nifty-knight/Sunrise-Alarm-Clock-2025/Images/Onshape Pictures/Screenshot 2025-08-16 090349.png

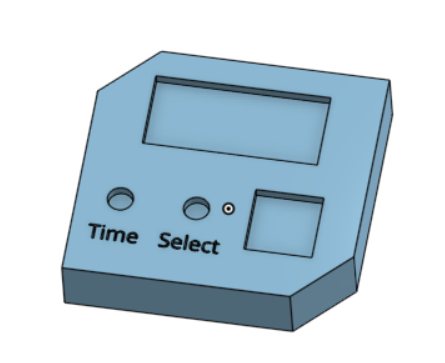
Images/Onshape Pictures/Screenshot 2025-08-16 090349.png
