nifty-knight/Sunrise-Alarm-Clock-2025/src/basic_lcd_print/basic_lcd_print.ino

// include the library
#include <LiquidCrystal.h>

// Creates an LCD object. Parameters: (rs, enable, d4, d5, d6, d7)
LiquidCrystal lcd(13, 11, 10, 8, 3, 2);

void setup() {
  // set up the LCD's number of columns and rows:
  lcd.begin(16, 2);
  // lcd.display();
  pinMode(A5, OUTPUT);
  digitalWrite(A5, 1);

  // Clears the LCD screen
  lcd.clear();
}

void loop() {
  // Print a message to the LCD.
  lcd.print(" Hello world!");

  // set the cursor to column 0, line 1
  // (note: line 1 is the second row, since counting begins with 0):
  lcd.setCursor(0, 1);
  // Print a message to the LCD.
  lcd.print(" LCD Tutorial");
}
