nifty-knight/Sunrise-Alarm-Clock-2025/src/Clock_Module_getTimeExample/Clock_Module_getTimeExample.ino

/** GetDateTime.cpp
 *
 * Example of getting the date and time from the RTC.
 *
 * @version 1.0.1
 * @author Rafa Couto <caligari@treboada.net>
 * @license GNU Affero General Public License v3.0
 * @see https://github.com/Treboada/Ds1302
 *
 */
#include <Arduino.h>
#include <Ds1302.h>

const int PIN_ENA = 5;
const int PIN_CLK = 7;
const int PIN_DAT = 6;

// DS1302 RTC instance
Ds1302 rtc(PIN_ENA, PIN_CLK, PIN_DAT);


const static char* WeekDays[] =
{
    "Monday",
    "Tuesday",
    "Wednesday",
    "Thursday",
    "Friday",
    "Saturday",
    "Sunday"
};


void setup()
{
    Serial.begin(9600);

    // initialize the RTC
    rtc.init();

    // test if clock is halted and set a date-time (see example 2) to start it
    if (rtc.isHalted())
    {
        Serial.println("RTC is halted. Setting time...");

        Ds1302::DateTime dt = {
            .year = 17,
            .month = Ds1302::MONTH_OCT,
            .day = 3,
            .hour = 4,
            .minute = 51,
            .second = 30,
            .dow = Ds1302::DOW_TUE
        };

        rtc.setDateTime(&dt);
    }
}


void loop()
{
    // get the current time
    Ds1302::DateTime now;
    rtc.getDateTime(&now);

    static uint8_t last_second = 0;
    if (last_second != now.second)
    {
        last_second = now.second;

        Serial.print("20");
        Serial.print(now.year);    // 00-99
        Serial.print('-');
        if (now.month < 10) Serial.print('0');
        Serial.print(now.month);   // 01-12
        Serial.print('-');
        if (now.day < 10) Serial.print('0');
        Serial.print(now.day);     // 01-31
        Serial.print(' ');
        Serial.print(WeekDays[now.dow - 1]); // 1-7
        Serial.print(' ');
        if (now.hour < 10) Serial.print('0');
        Serial.print(now.hour);    // 00-23
        Serial.print(':');
        if (now.minute < 10) Serial.print('0');
        Serial.print(now.minute);  // 00-59
        Serial.print(':');
        if (now.second < 10) Serial.print('0');
        Serial.print(now.second);  // 00-59
        Serial.println();
    }

    delay(100);
}
